hipsonmk-hub/CC-O4-Centauro-Aracnido/1781386406446.png

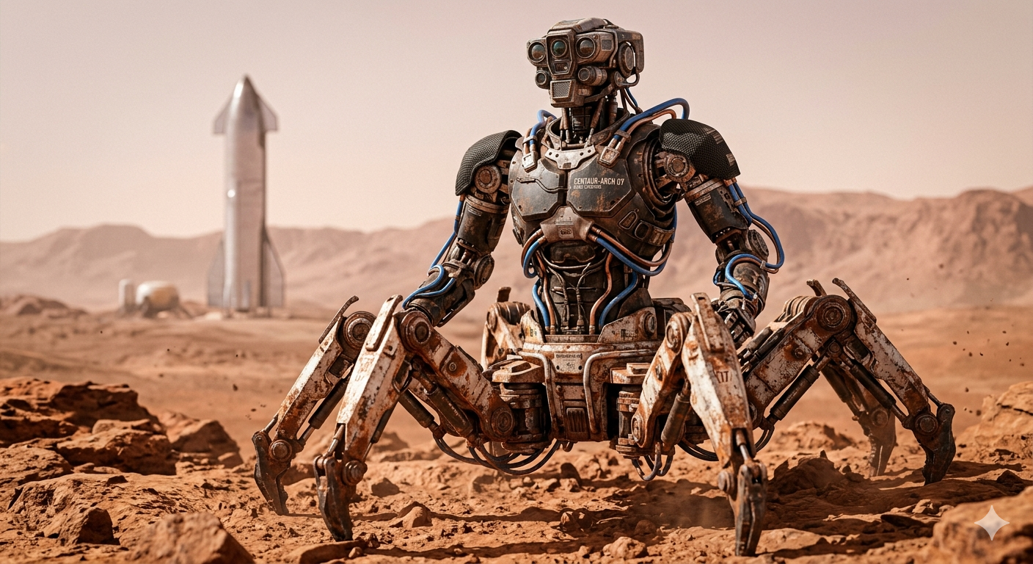
1781386406446.png
