hipsonmk-hub/CC-O4-Centauro-Aracnido/image-2.jpg

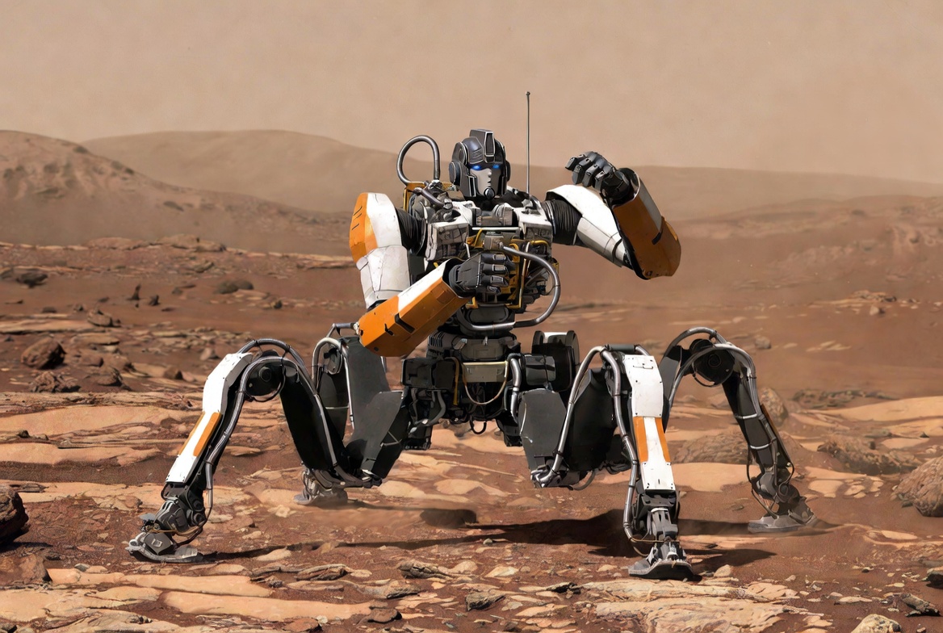
image-2.jpg
