hipsonmk-hub/CC-O4-Centauro-Aracnido/image-6.jpg

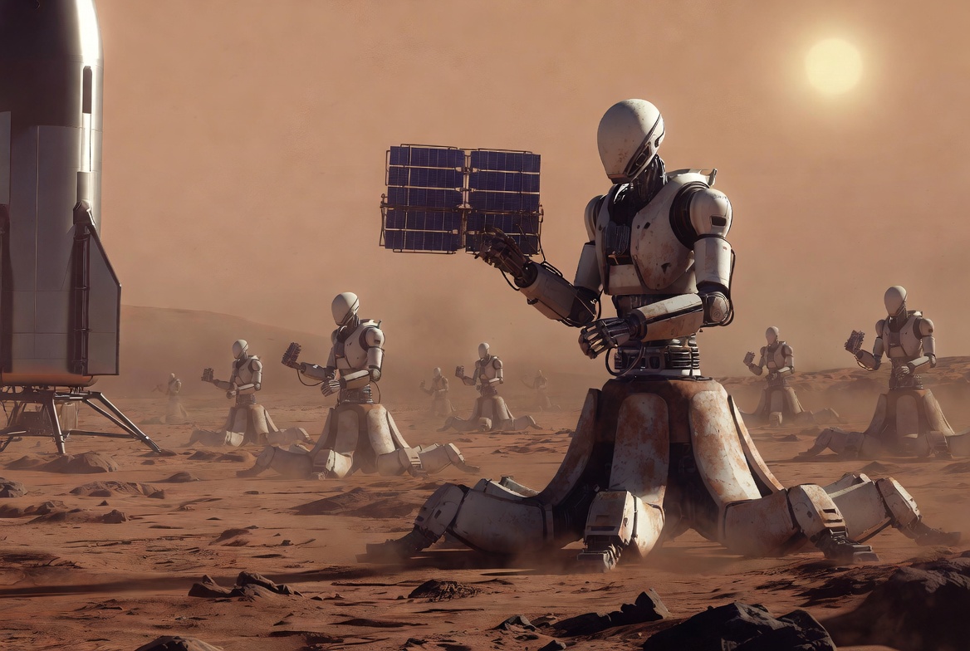
image-6.jpg
